iamericmin/Time-Machine-Mk.-7/technical drawings/tm7_revG_top.pdf

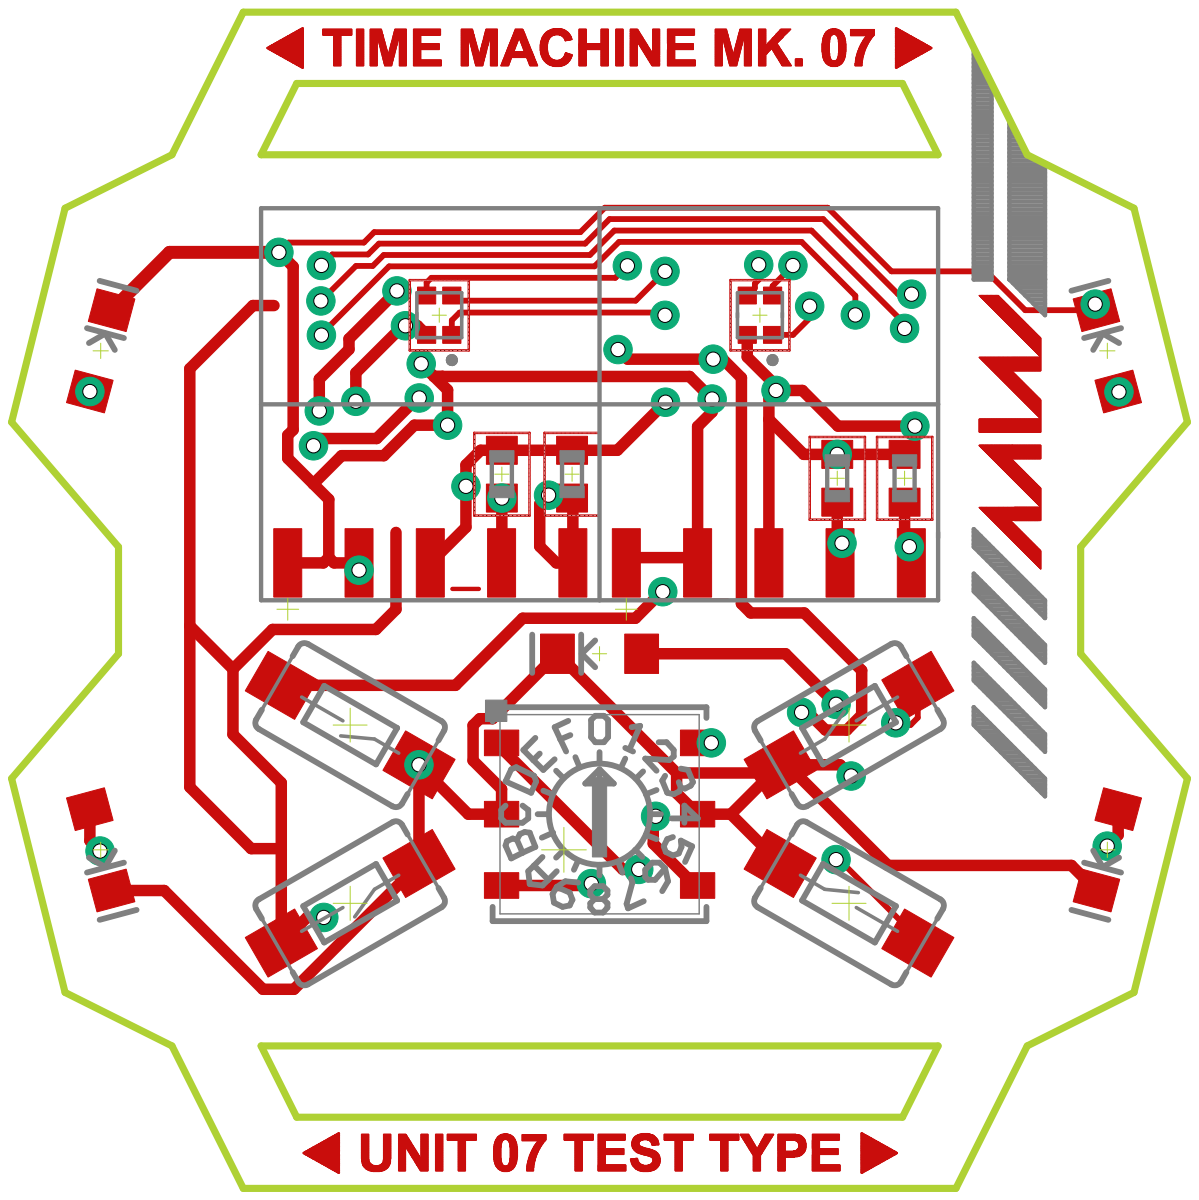
[picture p19: page 1]
