iamericmin/Time-Machine-Mk.-7/technical drawings/tm7_revG_top_actualSize.pdf

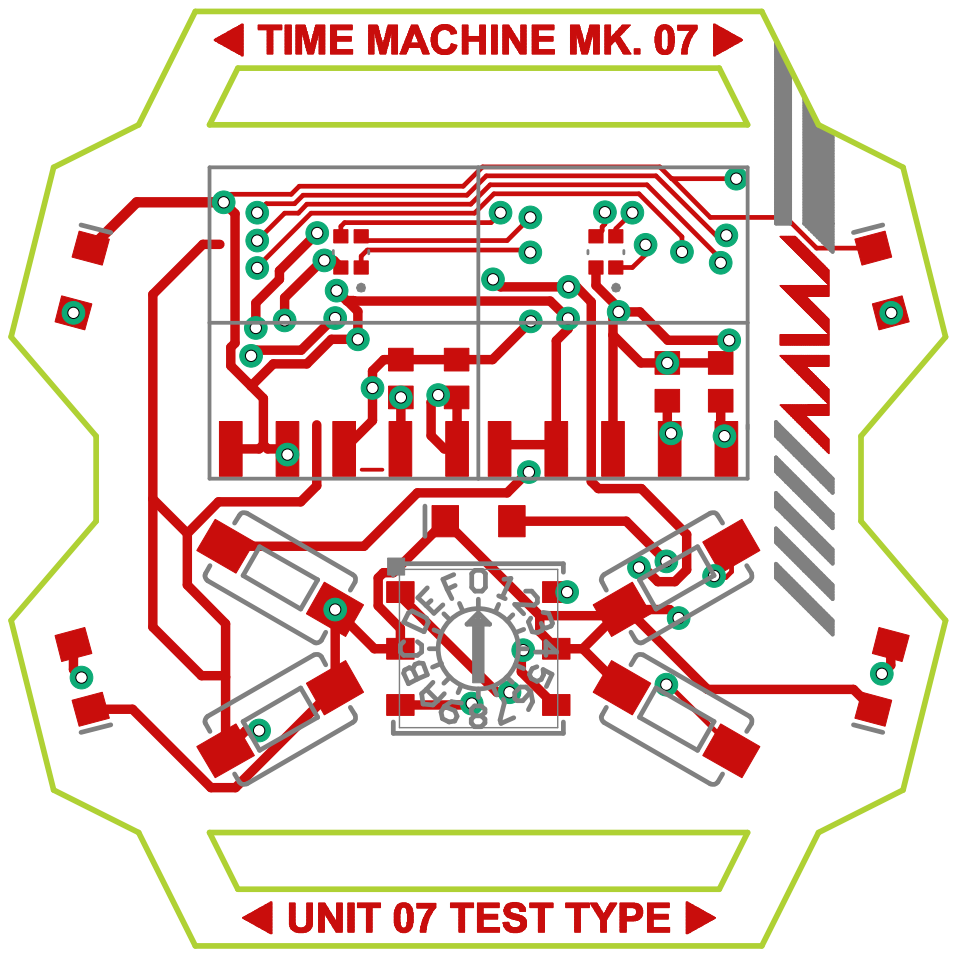
[picture p20: page 1]
