iamericmin/Time-Machine-Mk.-7/technical drawings/tm7_revG_top_black.pdf

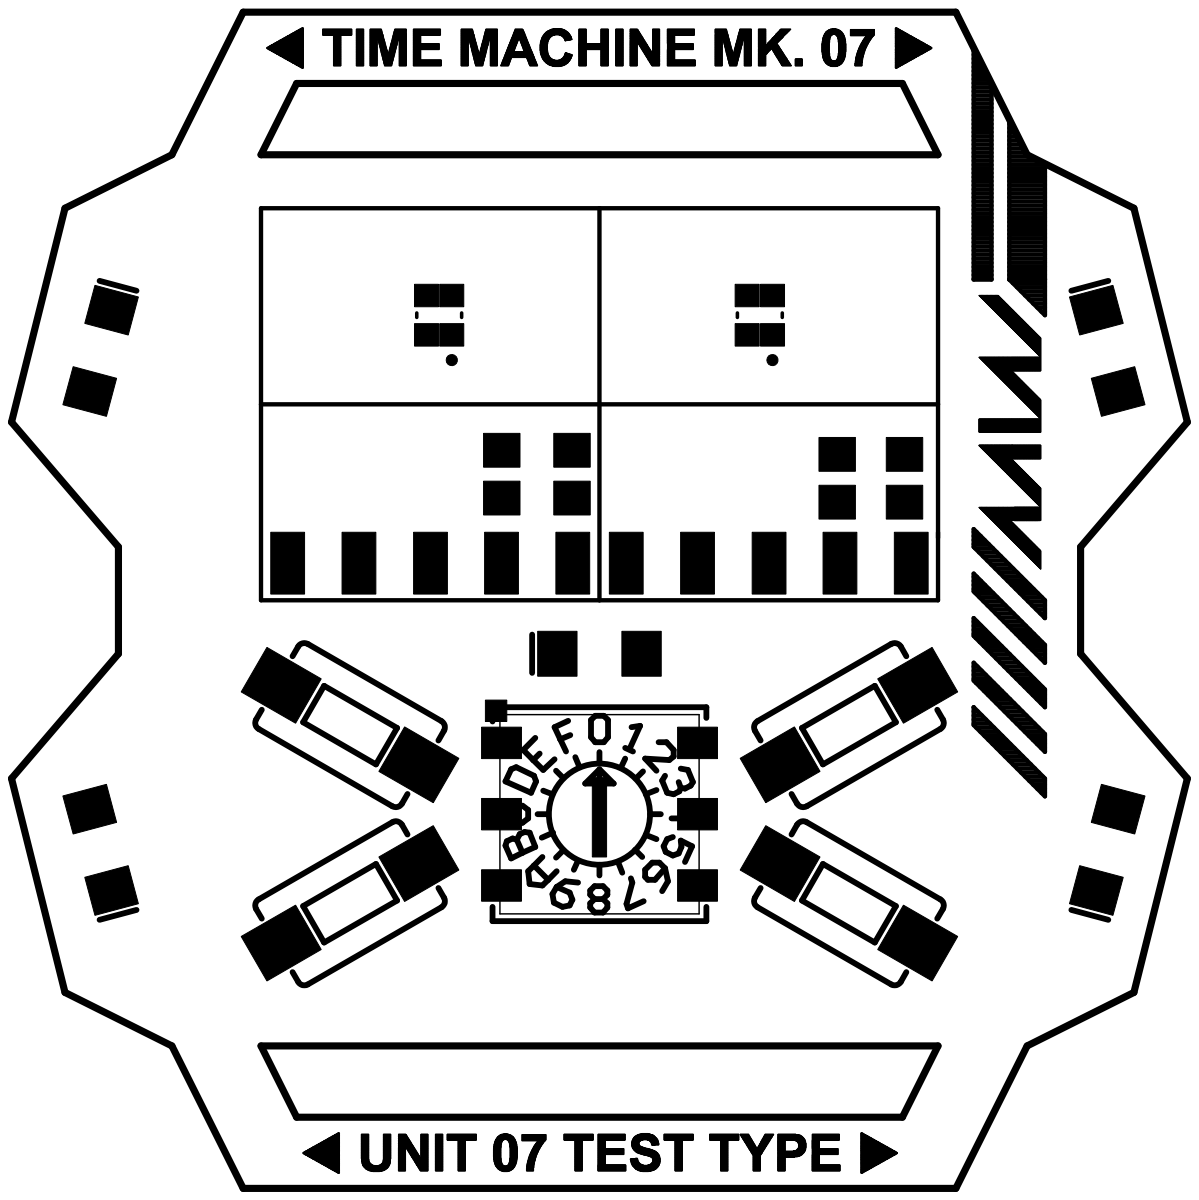
[picture p21: page 1]
