iamericmin/Time-Machine-Mk.-7/technical drawings/tm7_revG_top_black_2x.pdf

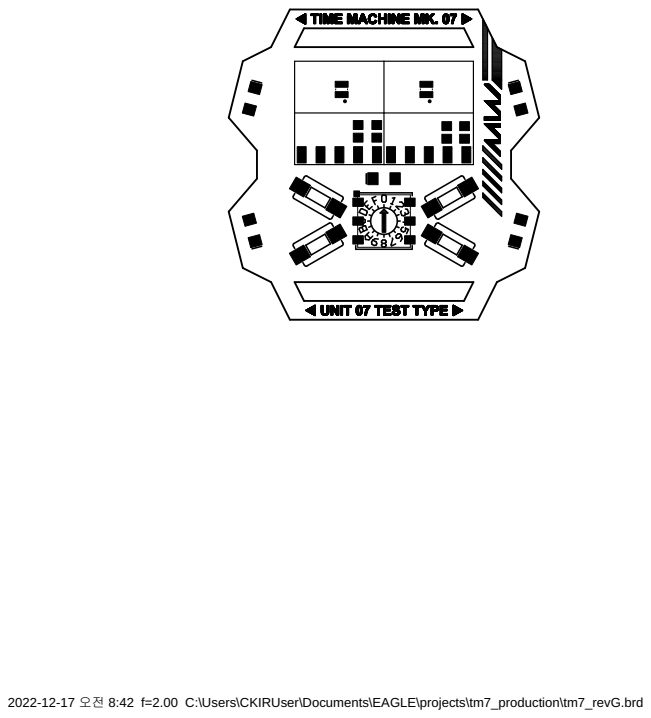
[picture p22: page 1]

2022-12-17 오전 8:42 f=2.00 C:\Users\CKIRUser\Documents\EAGLE\projects\tm7_production\tm7_revG.brd
