iamericmin/Time-Machine-Mk.-7/technical drawings/tm7_revG_top_black_actualSize.pdf

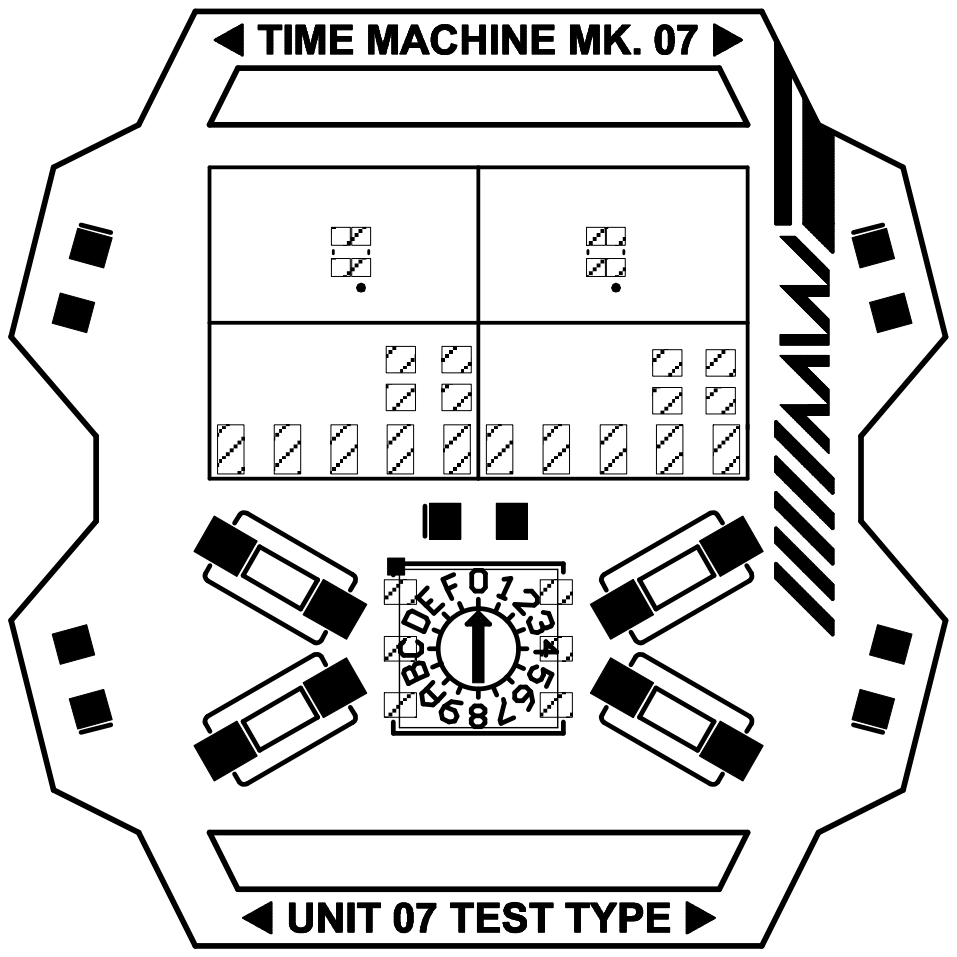
[picture p23: page 1]
