iamericmin/Time-Machine-Mk.-7/cutting board/tm7_TimeAttack.brd

## EAGLE design cutting board/tm7_TimeAttack.brd (2023-03-25)

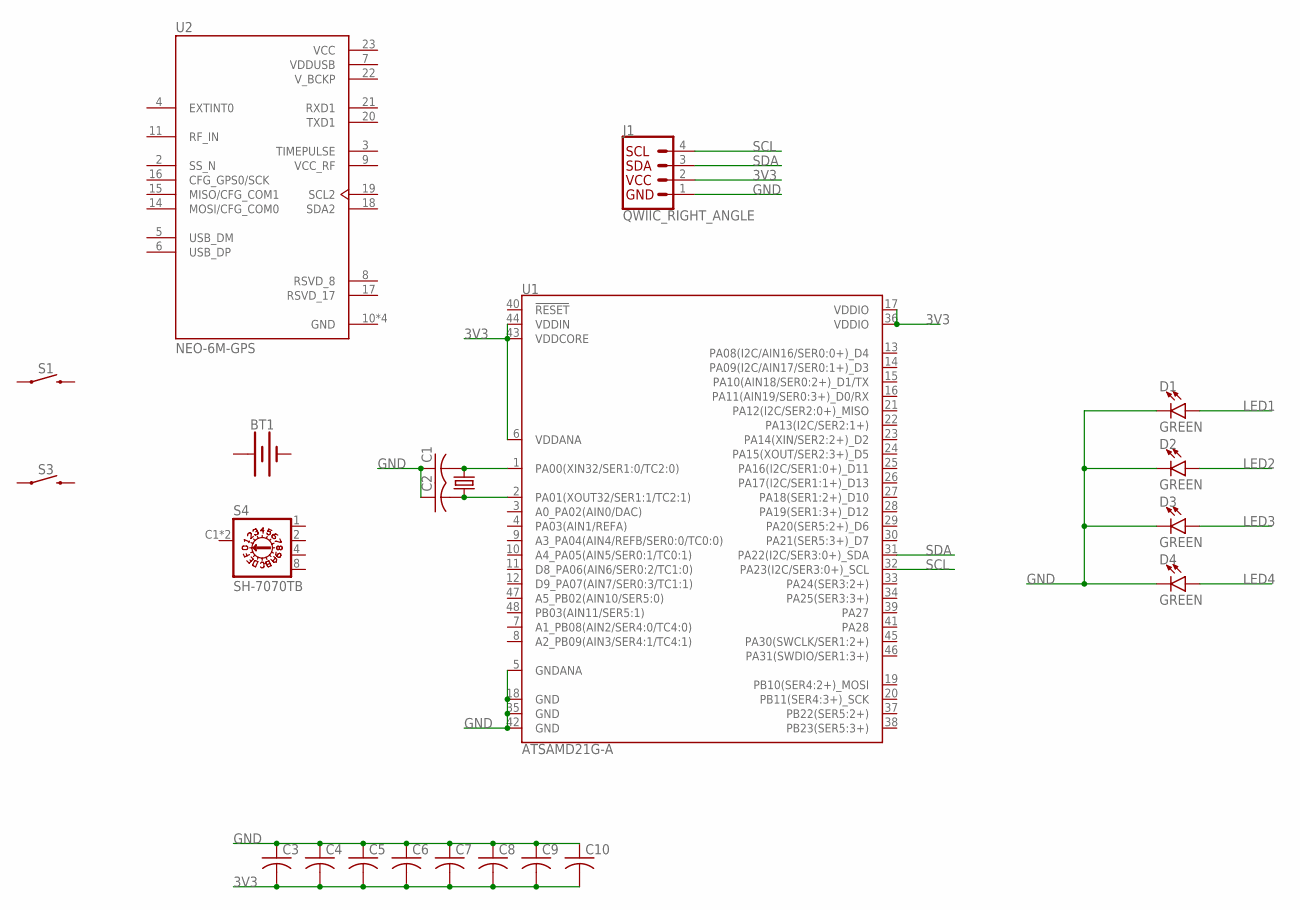
[picture p32: schematic tm7_TimeAttack.sch]

Parts:
BT1: BATTERY-20MM_SMD_4LEGS_OVERPASTE_INNER; BATTCON_20MM_4LEGS_OVERPASTE_INNER
C1, C2, C3, C4, C5, C6, C7, C8, C9, C10: C-USC0402; C0402
D1, D2, D3, D4: GREEN; LED-1206
J1: QWIIC_RIGHT_ANGLE; JST04_1MM_RA
S1, S3: MOMENTARY-SWITCH-SPST-SMD-6.2MM-TALL; TACTILE_SWITCH_SMD_6.2MM_TALL
S4: SH-7070TB; SH-7070B
U1: ATSAMD21G-A; TQFP-48
U2: NEO-6M-GPS; XCVR_NEO-6M-GPS
Y1: 32.768kHz; CRYSTAL-SMD-3.2X1.5MM

Connections:
3V3: C3.2, C4.2, C5.2, C6.2, C7.2, C8.2, C9.2, C10.2, J1.2, U1.6 (VDDANA), U1.17 (VDDIO), U1.36 (VDDIO), U1.43 (VDDCORE), U1.44 (VDDIN)
+: BT1.1 (+)
-: BT1.2 (-)
GND: C1.1, C2.1, C3.1, C4.1, C5.1, C6.1, C7.1, C8.1, C9.1, C10.1, D1.C, D2.C, D3.C, D4.C, J1.1, U1.5 (GNDANA), U1.18 (GND), U1.35 (GND), U1.42 (GND), U2.10 (GND), U2.12 (GND), U2.13 (GND), U2.24 (GND)
LED1: D1.A
LED2: D2.A
LED3: D3.A
LED4: D4.A
unnamed: C1.2, U1.1 (PA00(XIN32/SER1:0/TC2:0)), Y1.P$2 (2)
unnamed: C2.2, U1.2 (PA01(XOUT32/SER1:1/TC2:1)), Y1.P$1 (1)
SCL: J1.4, U1.32 (PA23(I2C/SER3:0+)_SCL)
SDA: J1.3, U1.31 (PA22(I2C/SER3:0+)_SDA)
VCC: U2.23 (VCC)
VDDUSB: U2.7 (VDDUSB)
V_BCKP: U2.22 (V_BCKP)

Board: 2 copper layers, 22 parts (15 on the bottom side), 6 nets, no tracks yet.
